ginkgo/trackball/step/adapter.step

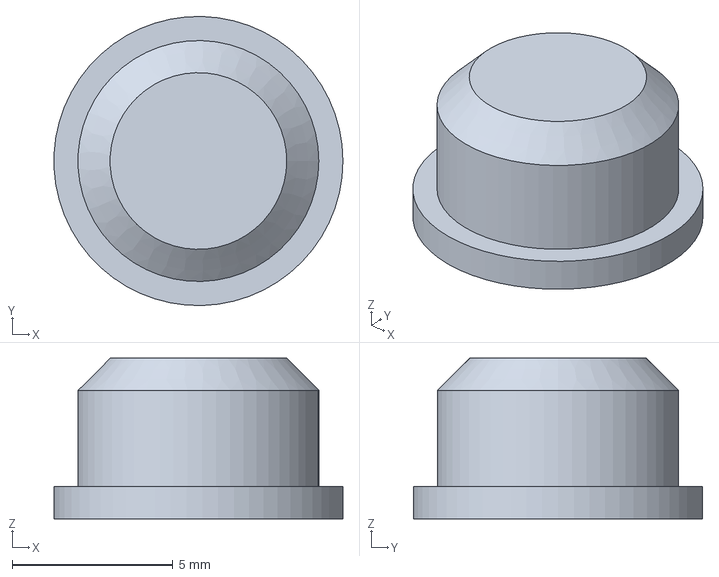
[picture p31: CAD file, 2024-11-24, last stored version]
step/adapter.step
8.99 x 9.00 x 5.00 mm
